StarGate01/power-extender/software/power-extender-raspberrypi/pypowerextender/PCA9557_Registers.py

## @package pypowerextender
# @file PCA9557_Registers.py
# @author Christoph Honal
# @brief Defines the needed registers for the PCA9557
# @version 0.0.1
# @date 2021-07-20


PCA9557_REG_CONTROL_INPUT_PORT = 0x00
PCA9557_REG_CONTROL_OUTPUT_PORT = 0x01
PCA9557_REG_CONTROL_POLARITY_INVERSION = 0x02
PCA9557_REG_CONTROL_CONFIGURATION = 0x03
